open-ephys/onix-headstage-64/spice/howland-ADA4062-tran.asc

C1: cap; 300nF
R1: res; 1K; tol=0.05
R2: res; 1Meg
R3: res; 10k
R4: res; 2.86k
R5: res; 10k; tol=0.05
R6: res; 10k; tol=0.05
R7: res; 1k
R8: res; 100; tol=1
R9: res; 10k; tol=0.05
R10: res; 9K; tol=0.05
R11: res; 10k; tol=0.05
R12: res; 10k; tol=0.05
R13: res; 10k; tol=0.05
R14: res; 10k; tol=0.05
R15: res; 10k; tol=0.05
R16: res; 10k; tol=1
R17: res; 10k; tol=1
U1: opamp2; ADA4062-2
U2: opamp2; ADA4062-2
U3: opamp2; ADA4062-2
U4: opamp2; ADA4062-2
V1: voltage; +15V
V2: voltage; -15V
V3: voltage; PWL(0 2.5 100u 2.5 101u {Vcmd} 200u {Vcmd} 201u 0 300u 0 301u 2.5)
V4: voltage; +3.3
V5: voltage; +2.5
Named nets: vin, v+, v-, 0, 3v3, 2v5, Imeas
.tran 0.5m
.step param Vcmd 0.1 5 1
Electrode
.inc ada4062-2.cir
Total area: 17x 0201s (.45 x0.9) + 1x LFCSP (3x3) = 15.8 mm2
